maugsburger/avr-component-tester/tester_bot.png

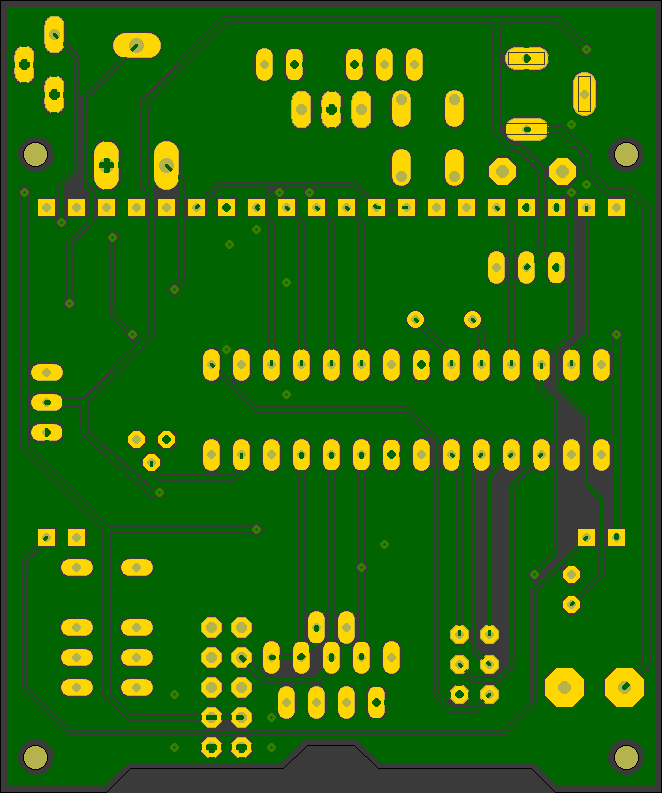
tester_bot.png
