maugsburger/avr-component-tester/tester_sheet1.png

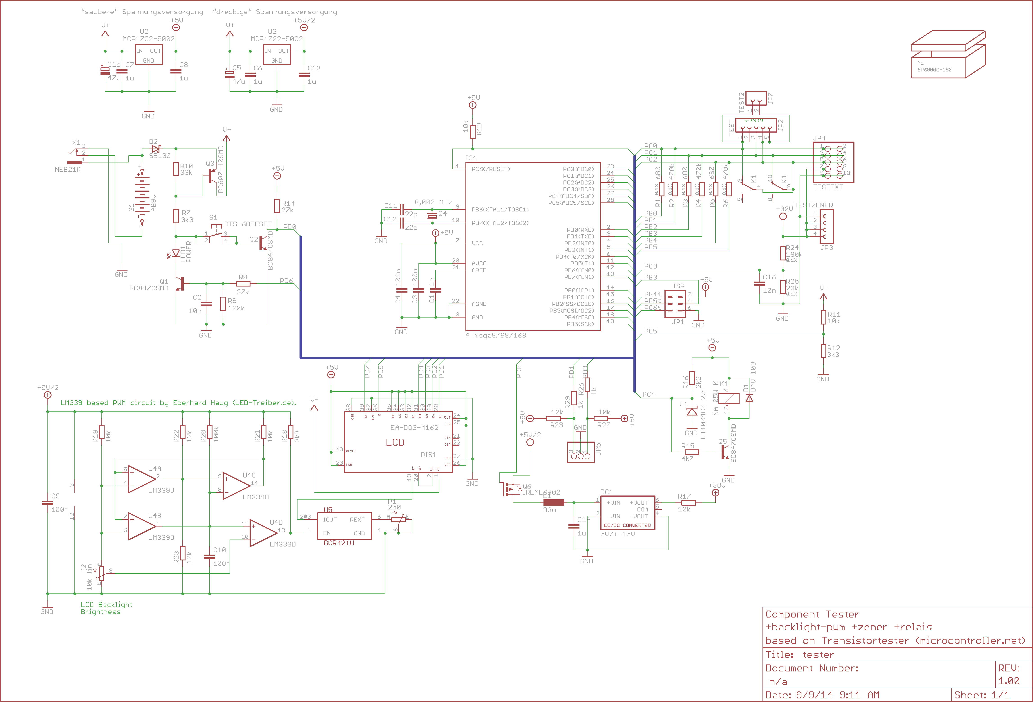
tester_sheet1.png
