maugsburger/avr-component-tester/tester_top.png

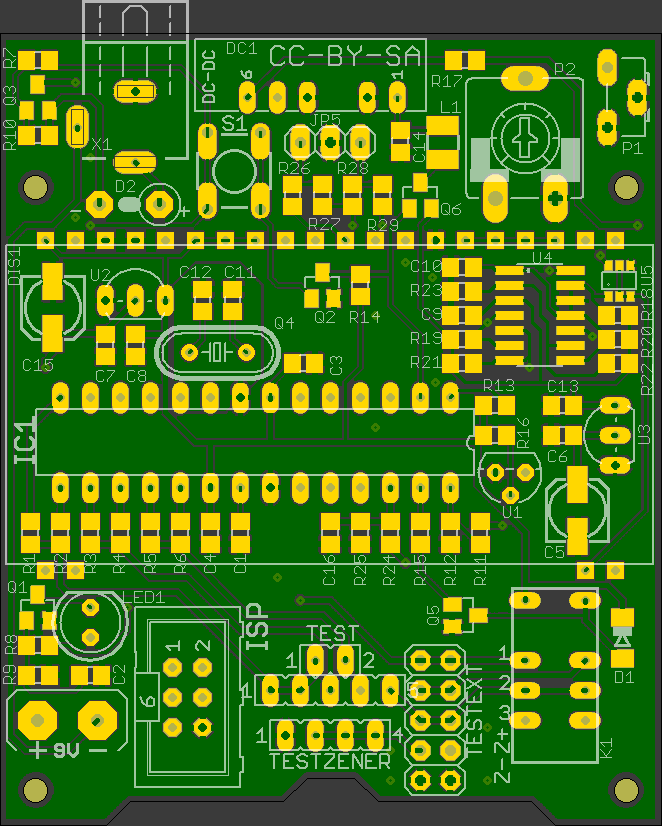
tester_top.png
